zettrik/ring_the_bell/prototype/data/images/win_animation.gif

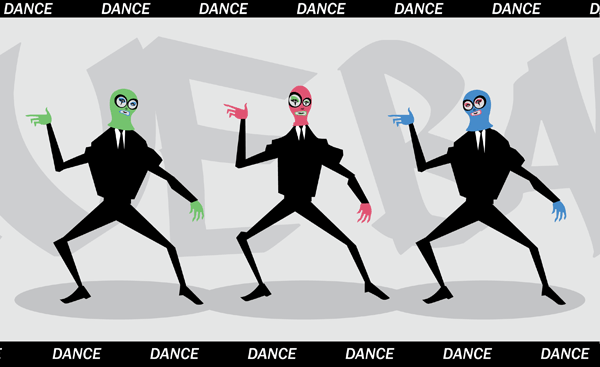
prototype/data/images/win_animation.gif
